larryli/switch/server_data.h

///
// server_data.h
//

static const char _server_last[] = "Fri, 29 Sep 2017 00:00:00 GMT";

// favicon.ico
#define SERVER_FAVICON_LEN 230
#define SERVER_FAVICON_ETAG "6539cd"
static const uint8_t _server_favicon_data[] PROGMEM = {
 0x1F, 0x8B, 0x08, 0x00, 0x00, 0x00, 0x00, 0x00, 0x02, 0x0B, 0xED, 0x54, 0xB9, 0x11, 0xC2, 0x30,
 0x10, 0x5C, 0x1D, 0x36, 0x60, 0x63, 0x18, 0x47, 0xA4, 0x26, 0xA4, 0x04, 0x3F, 0xE5, 0x90, 0xF0,
 0x13, 0x10, 0x11, 0x51, 0x02, 0x1D, 0x40, 0x05, 0xFC, 0x4F, 0x09, 0x90, 0x51, 0x03, 0x33, 0x54,
 0x40, 0x66, 0x12, 0xE0, 0x6C, 0x31, 0xC8, 0x78, 0x86, 0x06, 0x18, 0xAF, 0x66, 0xEF, 0x6E, 0x6F,
 0x4F, 0xD2, 0x28, 0x11, 0x20, 0x78, 0xD9, 0x36, 0x62, 0x34, 0x75, 0xA0, 0xCA, 0xB9, 0xCE, 0x8C,
 0x5A, 0x35, 0xA6, 0x40, 0x51, 0x9A, 0x02, 0x0A, 0x89, 0x7A, 0xD3, 0xF5, 0x30, 0x6F, 0xB9, 0xD8,
 0xF5, 0x02, 0x2C, 0x38, 0x2F, 0xDB, 0x2E, 0xD6, 0x1D, 0x1F, 0x87, 0x41, 0xC0, 0x9E, 0x8F, 0x6D,
 0xCF, 0xE7, 0x9E, 0x87, 0x55, 0xC4, 0x8E, 0x87, 0x7D, 0xDF, 0x67, 0xDF, 0x43, 0x86, 0x0C, 0x19,
 0xFE, 0x10, 0x42, 0x23, 0xD2, 0x3E, 0x1F, 0x84, 0x45, 0x24, 0x2C, 0x4B, 0x10, 0x59, 0xB1, 0x24,
 0xAA, 0xC8, 0x7E, 0x85, 0xB4, 0xD8, 0x2D, 0xA9, 0xC1, 0x52, 0x64, 0xAB, 0x73, 0xB8, 0x36, 0xE2,
 0xA1, 0x37, 0x34, 0x2A, 0x17, 0xC9, 0x54, 0xDA, 0xA4, 0xC2, 0x7B, 0x5E, 0xC5, 0xB4, 0x4E, 0x07,
 0xBE, 0xD6, 0x90, 0x65, 0x4E, 0xCF, 0x27, 0x6F, 0xFA, 0x42, 0x5A, 0xEB, 0xE6, 0x8F, 0xA7, 0x3E,
 0x9F, 0x40, 0xE8, 0x00, 0x97, 0x02, 0x70, 0xBA, 0x02, 0x93, 0x1B, 0x30, 0xBB, 0x03, 0x4E, 0x28,
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
 0xD8, 0x8C, 0xA6, 0x10, 0xB2, 0x35, 0xC6, 0x95, 0x33, 0xB2, 0x52, 0xBA, 0x8C, 0xB5, 0xB3, 0xE9,
 0x86, 0x2B, 0x69, 0xA4, 0x4F, 0x29, 0x21, 0xE1, 0x30, 0x4F, 0x2A, 0x0D, 0x2E, 0x0F, 0x07, 0xD1,
 0xCF, 0x7B, 0x38, 0x88, 0x47, 0x6D, 0x57, 0x77, 0x9F, 0xE0, 0x03, 0x00, 0x00,
};
