larryli/switch/oled_font.c

#include "oled_font.h"
/*
  Fontname: -wenquanyi-wenquanyi bitmap song-medium-r-normal--12-120-75-75-P-119-ISO10646-1
  Copyright: (null)
  Glyphs: 137/30503
  BBX Build Mode: 0
*/
const uint8_t oled_font[2086] U8G2_FONT_SECTION("oled_font") =
  "\211\0\3\2\4\4\4\4\5\13\15\0\376\10\376\12\377\1d\2\332\4% \5\0\230\26!\7\221\212"
  "\26\247\0\42\7\64\371\26\221)#\16\226\210\67Q\313\260D\275\14K\324\2$\17\245xV\331RQ"
  "\62QK\224\312\26\1%\20\226x\66Q\322EK\302\64\211\222.Z\2&\16\205\210VY\22%Y"
  "eJ\242H\11'\6\61\372\25\3(\13\263yVI\224D\335\242,)\14\263y\26Y\224E]\242"
  "$\2*\14u\210V\225\312AY\232\42\0+\13w\210xqm\30\262\270\6,\7\62z\26\212\2"
  "-\7\25\310\26\203\0.\6!\212\25\2/\14\304xvMY)+e\65\0\60\12\205\210\66K\346"
  "[\262\0\61\11\205\210\26c\237\6\1\62\13\205\210\66K\26\326\332\6\1\63\15\205\210\26C\32&k"
  "\30\16\12\0\64\16\206\210wZ\22u\311\222aL\23\0\65\15\205\210\26C\22\206C\32\206\203\2\66"
  "\15\205\210\66K\30\16IfK\26\0\67\13\205\210\26\203X\13\263\260\4\70\15\205\210\66K\246%K"
  "fK\26\0\71\15\205\210\66KfK\206PK\26\0:\7a\210\22\222\0;\11\202z\26C\254("
  "\0<\10\225\210\226Y\327\16=\10\65\270\26\203:\10>\11\225\210\26i\267\216\0?\15\225\210\66K"
  "\246\205\221\226Ca\4@\24\247xX[%\221\264DR\224\212R\221\22%\313&\0A\16\207\210x"
  "q\232\204IV\32\224T\15B\15\206\210\27\203\22\212\303\22\32\207\5C\14\206\210\67C\22\252\35\223"
  "!\1D\15\207\210\30\203\24&\251\307d\220\0E\13\205\210\26\307p\30\213\203\0F\13\205\210\26\307"
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
  "\246\311\60Da\32V\262\332\60\4\221M\36\273x\34\203\62(\345\244<\254Je\30\22%\314\222p"
  "P\302,\311\206%\323\222A\221\315\30\273x<\303\71\35\16R\343\60\204Qq\30r \36\316\351p"
  "\20\225\355\33\273x<\331\60\345\200\232\251\231\62\14\211\250iI&\325\224,\23\65\35\30\227b\30\272"
  "y\34\17a\216\304\303A*IC$\225\244!\222J\303;\22\377\37\20\266|<C\42\15\221\250\31"
  "\355\230(\1\0";
